Just4Stan/OpenRX/shared/sheets/esp32c3_sx1281_rx_core.kicad_sch

## KiCad design shared/sheets/esp32c3_sx1281_rx_core.kicad_sch (2026-03-23)

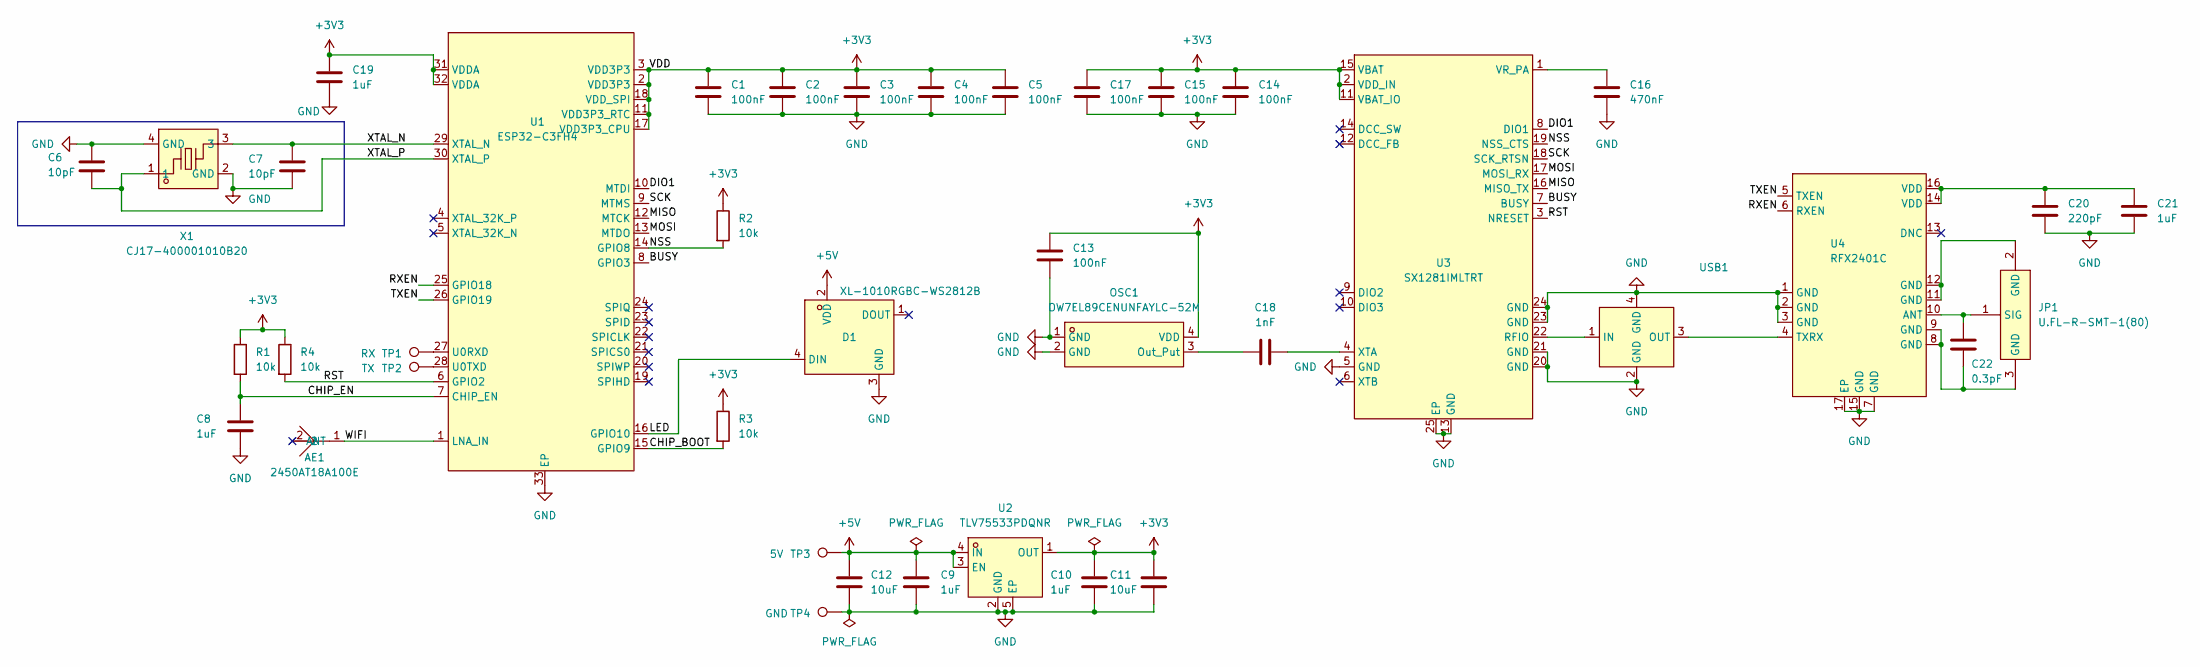
[picture p25: schematic esp32c3_sx1281_rx_core.kicad_sch]

Parts:
AE1: 2450AT18A100E; ANT-SMD_L3.2-W1.6; LCSC Part C89334
C1, C2, C3, C4, C5, C13, C14, C15, C17: 100nF; C_0201_0603Metric; LCSC C76939
C6, C7: 10pF; C_0201_0603Metric; LCSC C20069240
C8, C9, C10, C19, C21: 1uF; C_0201_0603Metric; LCSC C76935
C11, C12: 10uF; C_0201_0603Metric; LCSC C15525
C16: 470nF; C_0201_0603Metric; LCSC C85926
C18: 1nF; C_0201_0603Metric; LCSC C66942
C20: 220pF; C_0201_0603Metric
C22: 0.3pF; C_0201_0603Metric
D1: XL-1010RGBC-WS2812B; LED-SMD_4P-L1.0-W1.0-TL_XL-1010RGBC-WS2812B; LCSC Part C5349953
JP1: U.FL-R-SMT-1(80); RF-SMD_FRF05002-JSS103M; LCSC Part C88374
OSC1: OW7EL89CENUNFAYLC-52M; OSC-SMD_4P-L2.0-W1.6-BL_TXC_7Z; LCSC Part C22434896
R1, R2, R3, R4: 10k; R_0201_0603Metric; LCSC C106225
TP1: RX; SolderPad_1.0x1.5mm
TP2: TX; SolderPad_1.0x1.5mm
TP3: 5V; SolderPad_1.0x1.5mm
TP4: GND; SolderPad_1.0x1.5mm
U1: ESP32-C3FH4; QFN-32_L5.0-W5.0-P0.50-TL-EP3.7; LCSC Part C2858491
U2: TLV75533PDQNR; X2SON-4_L1.0-W1.0-P0.65-TL-EP; LCSC Part C2861882
U3: SX1281IMLTRT; QFN-24_L4.0-W4.0-P0.50-TL-EP2.6; LCSC Part C2151551
U4: RFX2401C; QFN-16_L3.0-W3.0-P0.50-BL-EP1.7; LCSC Part C19213
USB1: DEA102700LT-6307A2; FILTER-SMD_4P-L1.0-W0.5-L_DEA102700LT-XXX; LCSC Part C574024
X1: CJ17-400001010B20; CRYSTAL-SMD_4P-L1.6-W1.2-BL; LCSC Part C2875272

Connections:
+3V3: C1.1, C2.1, C3.1, C4.1, C5.1, C10.1, C11.1, C13.1, C14.1, C15.1, C17.1, C19.1, OSC1.4 (VDD), R1.1, R2.1, R3.1, R4.1, U1.2 (VDD3P3), U1.3 (VDD3P3), U1.11 (VDD3P3_RTC), U1.17 (VDD3P3_CPU), U1.18 (VDD_SPI), U1.31 (VDDA), U1.32 (VDDA), U2.1 (OUT), U3.2 (VDD_IN), U3.11 (VBAT_IO), U3.15 (VBAT)
+5V: C9.1, C12.1, D1.2 (VDD), TP3.1, U2.3 (EN), U2.4 (IN)
BUSY: U1.8 (GPIO3), U3.7 (BUSY)
CHIP_BOOT: R3.2, U1.15 (GPIO9)
CHIP_EN: C8.1, R1.2, U1.7 (CHIP_EN)
DIO1: U1.10 (MTDI), U3.8 (DIO1)
GND: C1.2, C2.2, C3.2, C4.2, C5.2, C6.2, C7.2, C8.2, C9.2, C10.2, C11.2, C12.2, C13.2, C14.2, C15.2, C16.2, C17.2, C19.2, C20.2, C21.2, D1.3 (GND), OSC1.1 (GND), OSC1.2 (GND), TP4.1, U1.33 (EP), U2.2 (GND), U2.5 (EP), U3.5 (GND), U3.13 (GND), U3.20 (GND), U3.21 (GND), U3.23 (GND), U3.24 (GND), U3.25 (EP), U4.1 (GND), U4.2 (GND), U4.3 (GND), U4.7 (GND), U4.15 (GND), U4.17 (EP), USB1.2 (GND), USB1.4 (GND), X1.2 (GND), X1.4 (GND)
LED: D1.4 (DIN), U1.16 (GPIO10)
MISO: U1.12 (MTCK), U3.16 (MISO_TX)
MOSI: U1.13 (MTDO), U3.17 (MOSI_RX)
NSS: R2.2, U1.14 (GPIO8), U3.19 (NSS_CTS)
unnamed: C16.1, U3.1 (VR_PA)
unnamed: C18.1, OSC1.3 (Out_Put)
unnamed: C18.2, U3.4 (XTA)
unnamed: C20.1, C21.1, U4.14 (VDD), U4.16 (VDD)
unnamed: C22.1, JP1.1 (SIG), U4.10 (ANT)
unnamed: C22.2, JP1.3 (GND), U4.8 (GND), U4.9 (GND)
unnamed: JP1.2 (GND), U4.11 (GND), U4.12 (GND)
unnamed: TP1.1, U1.27 (U0RXD)
unnamed: TP2.1, U1.28 (U0TXD)
unnamed: U3.22 (RFIO), USB1.1 (IN)
unnamed: U4.4 (TXRX), USB1.3 (OUT)
RST: R4.2, U1.6 (GPIO2), U3.3 (NRESET)
RXEN: U1.25 (GPIO18), U4.6 (RXEN)
SCK: U1.9 (MTMS), U3.18 (SCK_RTSN)
TXEN: U1.26 (GPIO19), U4.5 (TXEN)
WIFI: AE1.1 (ANT), U1.1 (LNA_IN)
XTAL_N: C7.1, U1.29 (XTAL_N), X1.3
XTAL_P: C6.1, U1.30 (XTAL_P), X1.1
